irakhlin/zigbee-climate-sensor/docs/image1.jpg

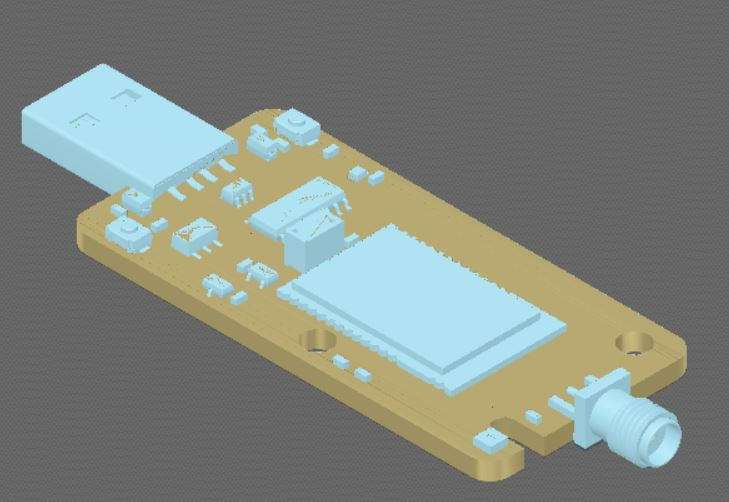
docs/image1.jpg
